dczia/yolobadge/Hardware/Images/Back Label Top.png

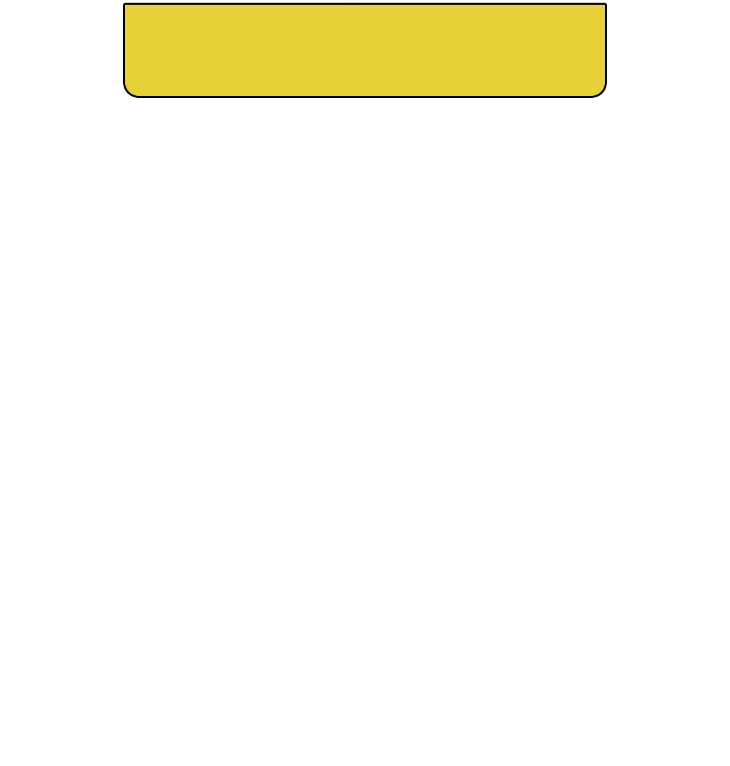
Hardware/Images/Back Label Top.png
