dczia/yolobadge/Hardware/Images/Back Outline.png

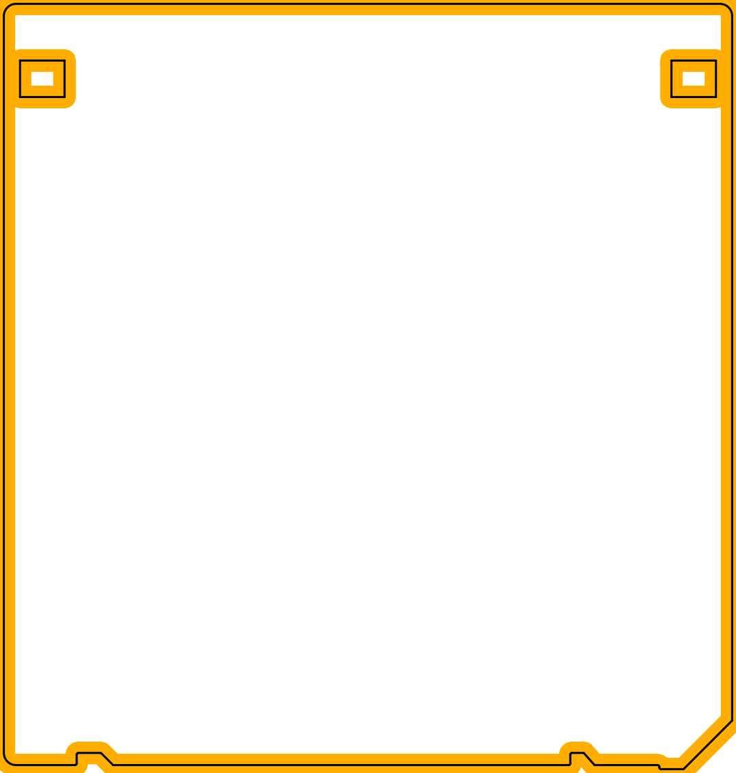
Hardware/Images/Back Outline.png
