dczia/yolobadge/Hardware/Images/Back Slide.png

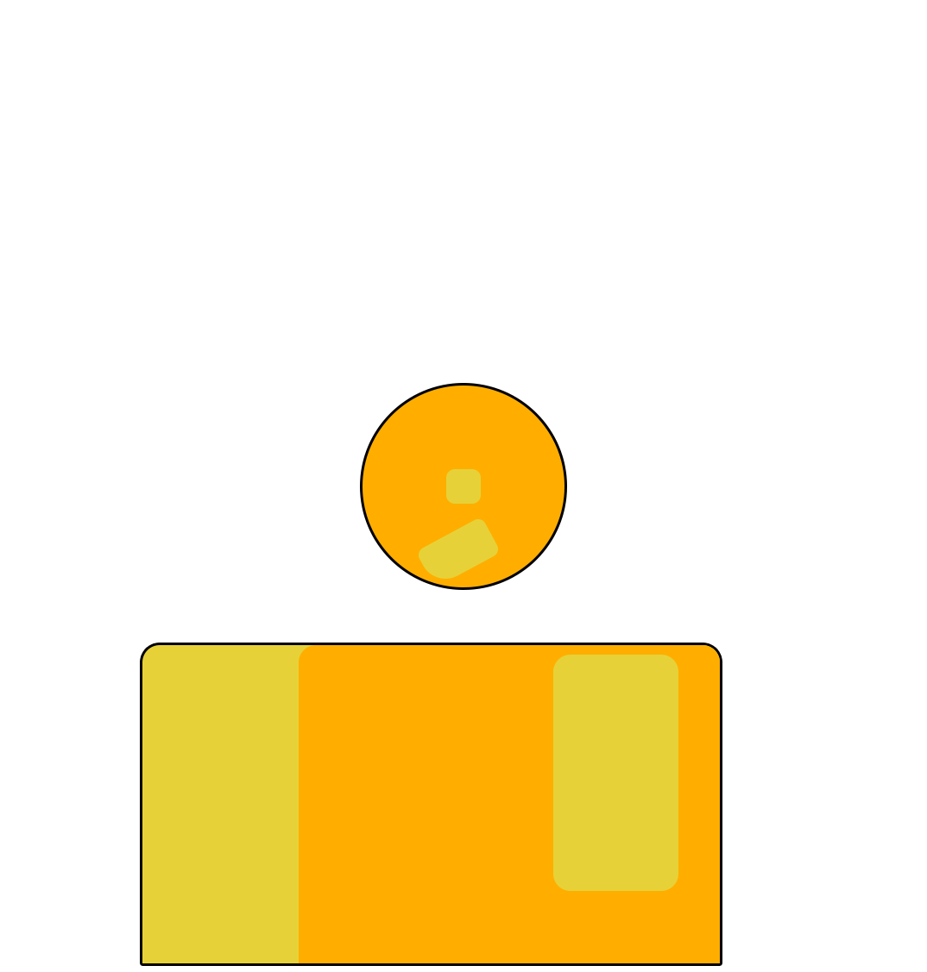
Hardware/Images/Back Slide.png
