dczia/yolobadge/Hardware/Images/board outline.png

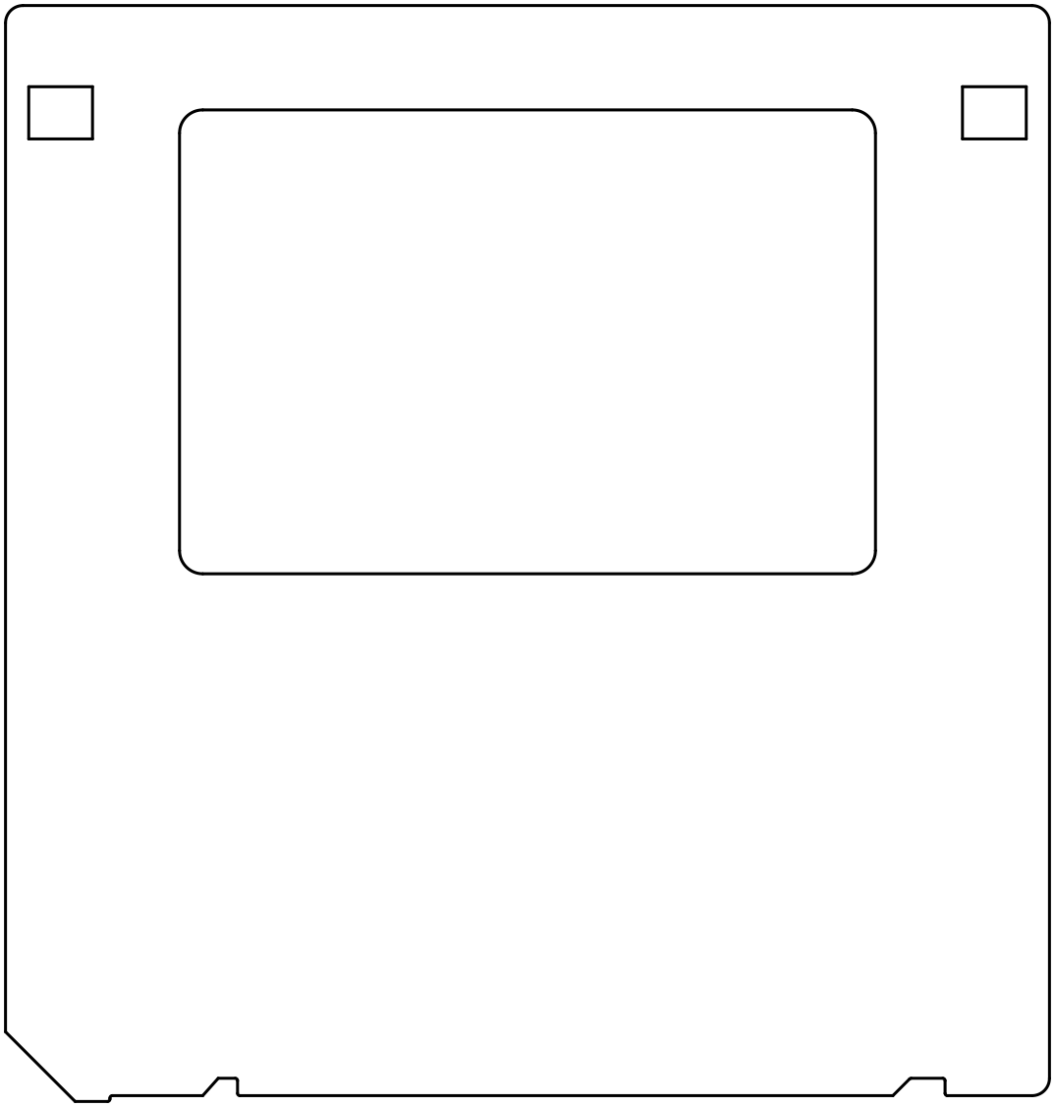
Hardware/Images/board outline.png
