dczia/yolobadge/Hardware/Images/slide text.png

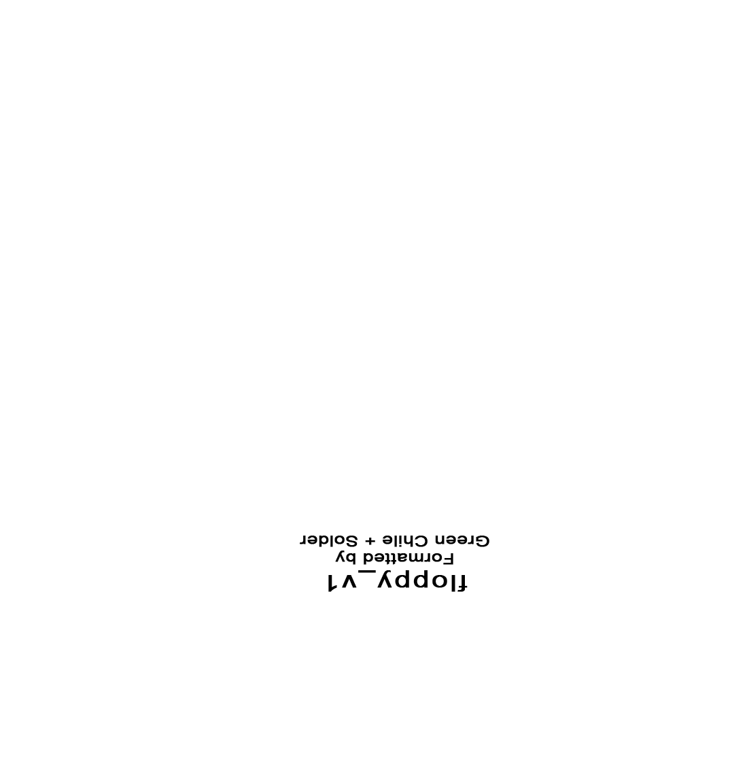
Hardware/Images/slide text.png
