dczia/yolobadge/Hardware/Images/Slide.png

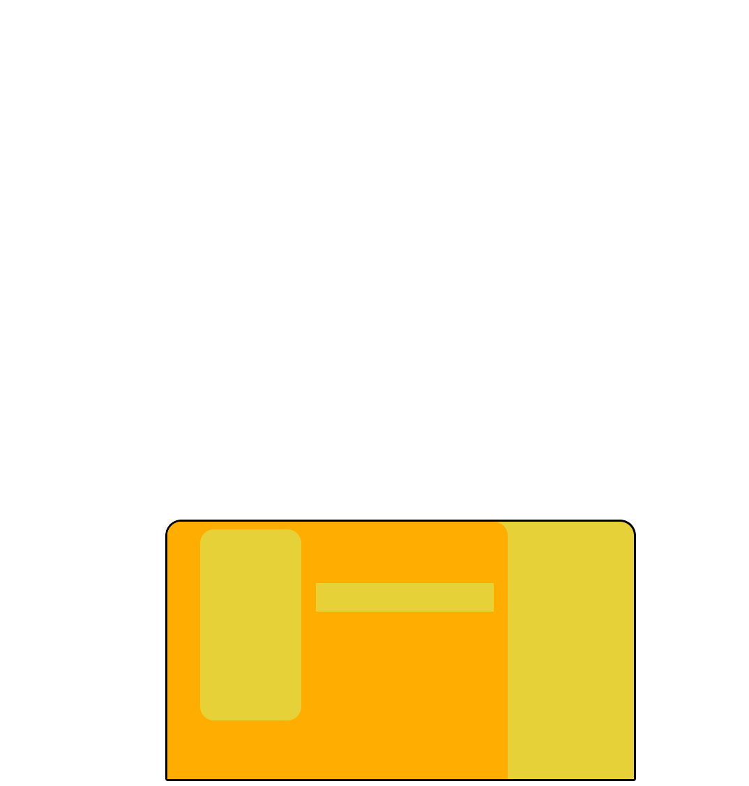
Hardware/Images/Slide.png
