dczia/yolobadge/Hardware/Images/zia background.png

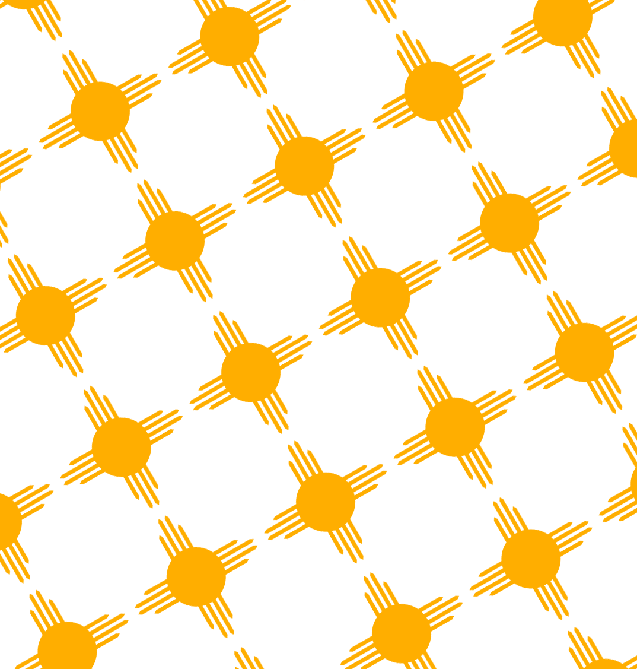
Hardware/Images/zia background.png
