dczia/yolobadge/Hardware/Images/zia label.png

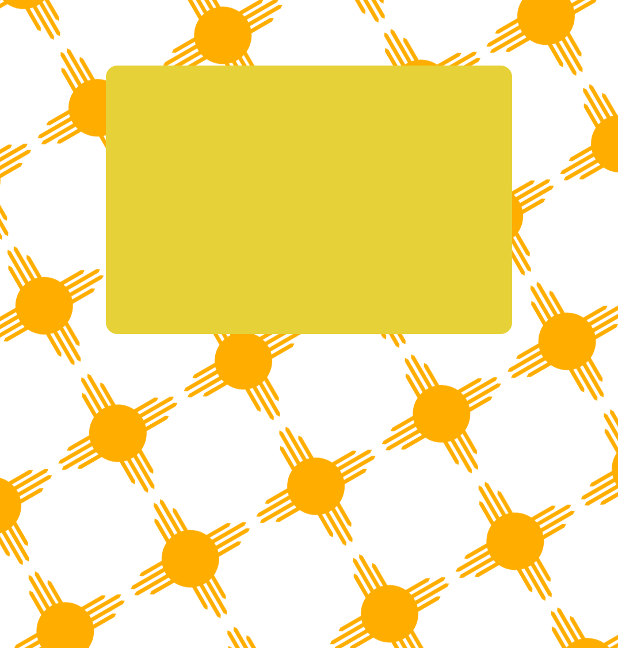
Hardware/Images/zia label.png
